yangzigy/yz_keyboard/f103vbt6/hal/f1_uart.h

/*
uart.h
同步方式的串口通信
*/
#ifndef F1_UART_H
#define F1_UART_H

#include "main.h"
#include "stm32f1_sys.h"
#include "queue.h"

typedef struct
{
	USART_TypeDef *uart;
	Queue que_tx;
	Queue que_rx;
} S_UART; //串口设备结构

extern S_UART uart1;
extern S_UART uart2;
extern S_UART uart3;
extern S_UART uart4;
extern S_UART uart5; //串口对象

void uart_irq(S_UART *obj);
void uart_initial(S_UART *obj,int b);
void uart_send(u8 *p,int n,S_UART *obj); //发送数据

int uart1_putchar(int c);

#endif
